Canditos/WELDEDSID_DASHBOARD/3d-enclosure/preview.png

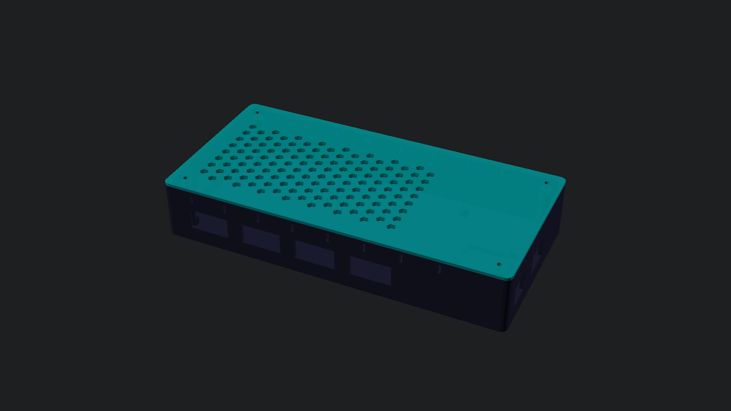
3d-enclosure/preview.png
