Canditos/WELDEDSID_DASHBOARD/3d-enclosure/preview_pcbs.png

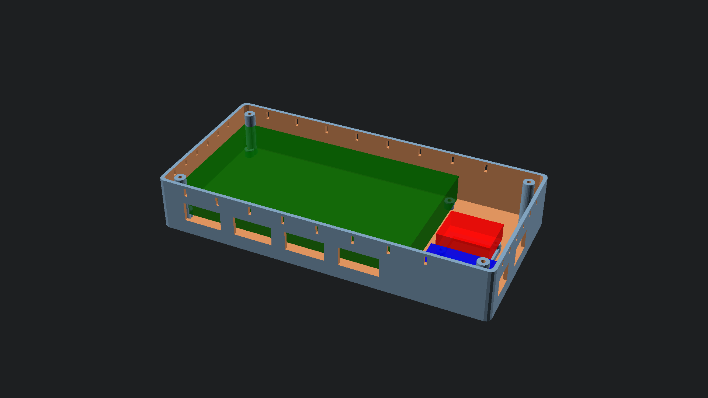
3d-enclosure/preview_pcbs.png
