Canditos/WELDEDSID_DASHBOARD/data/charger.png

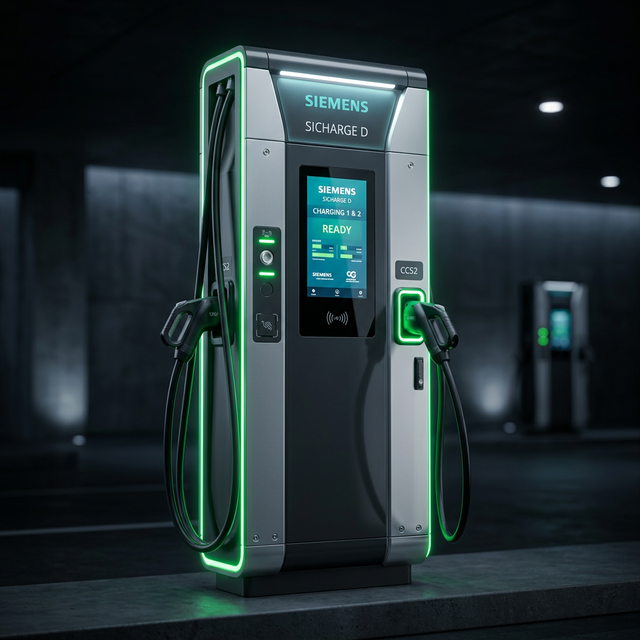
data/charger.png
